mbarszcz-pcb/arcader-usb/images/pcb/arcader-usb-render-bottom.PNG

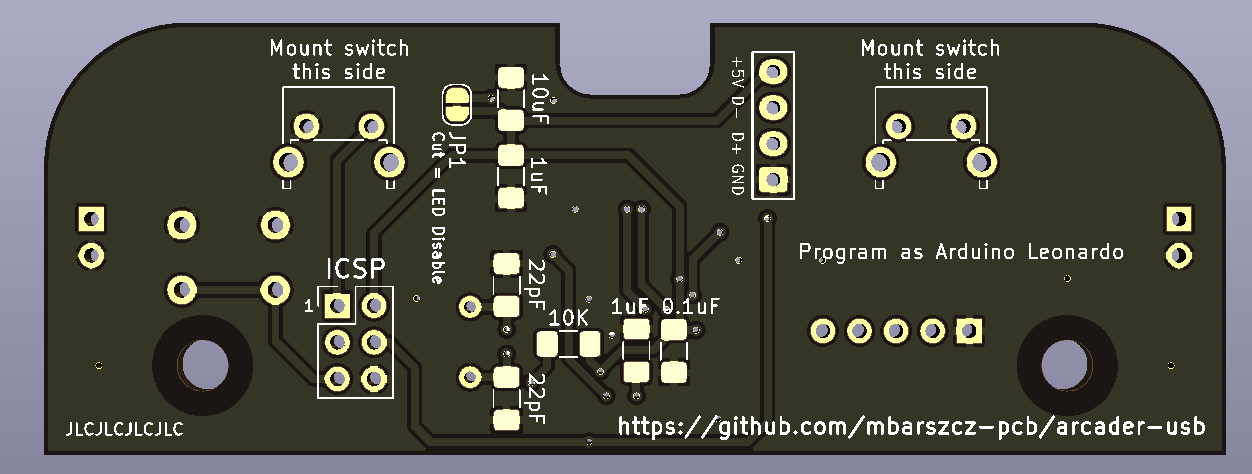
images/pcb/arcader-usb-render-bottom.PNG
