mbarszcz-pcb/arcader-usb/images/photos/PXL_20210202_015024054_copy.jpg

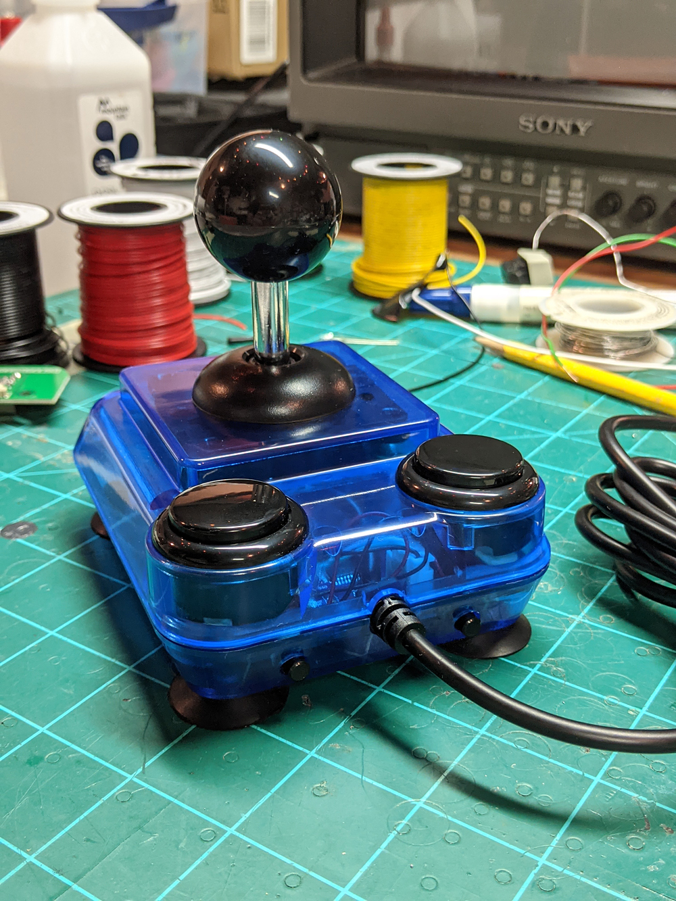
images/photos/PXL_20210202_015024054_copy.jpg
